8BitMixtape/8Bitmixtape_reworked/photos/digilog_version_v02.png

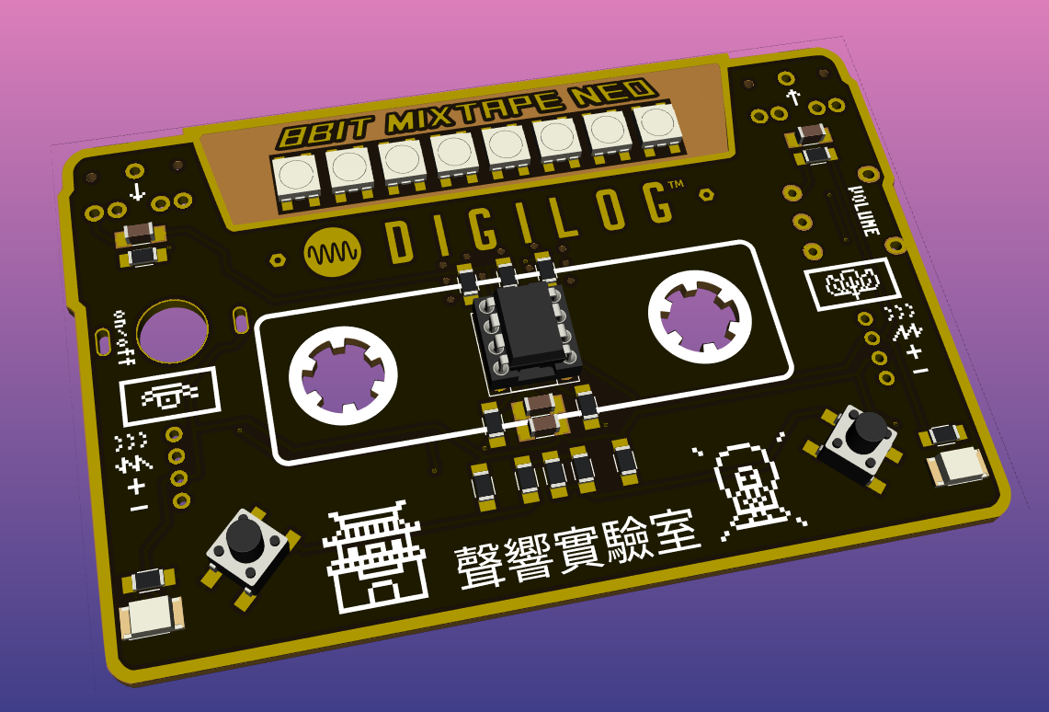
photos/digilog_version_v02.png
