8BitMixtape/8Bitmixtape_reworked/photos/digilog_version_v03.png

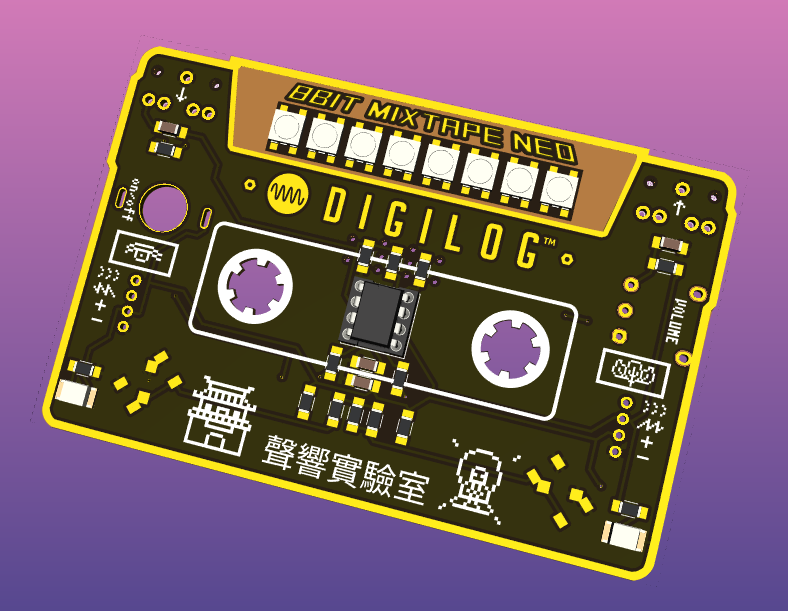
photos/digilog_version_v03.png
