8BitMixtape/8Bitmixtape_reworked/photos/pixelache_version_v01_noParts.png

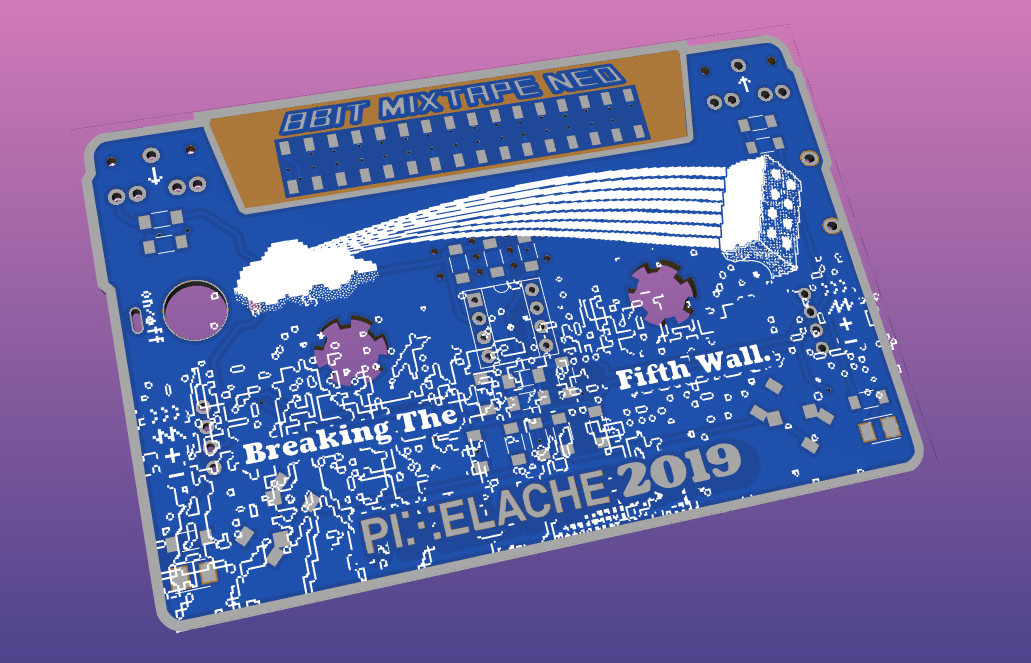
photos/pixelache_version_v01_noParts.png
